RamiroChac0n/P1_ORGA_G-12/Kicad/Práctica1 Lab.kicad_sch

## KiCad design Kicad/Práctica1 Lab.kicad_sch (2024-06-10)

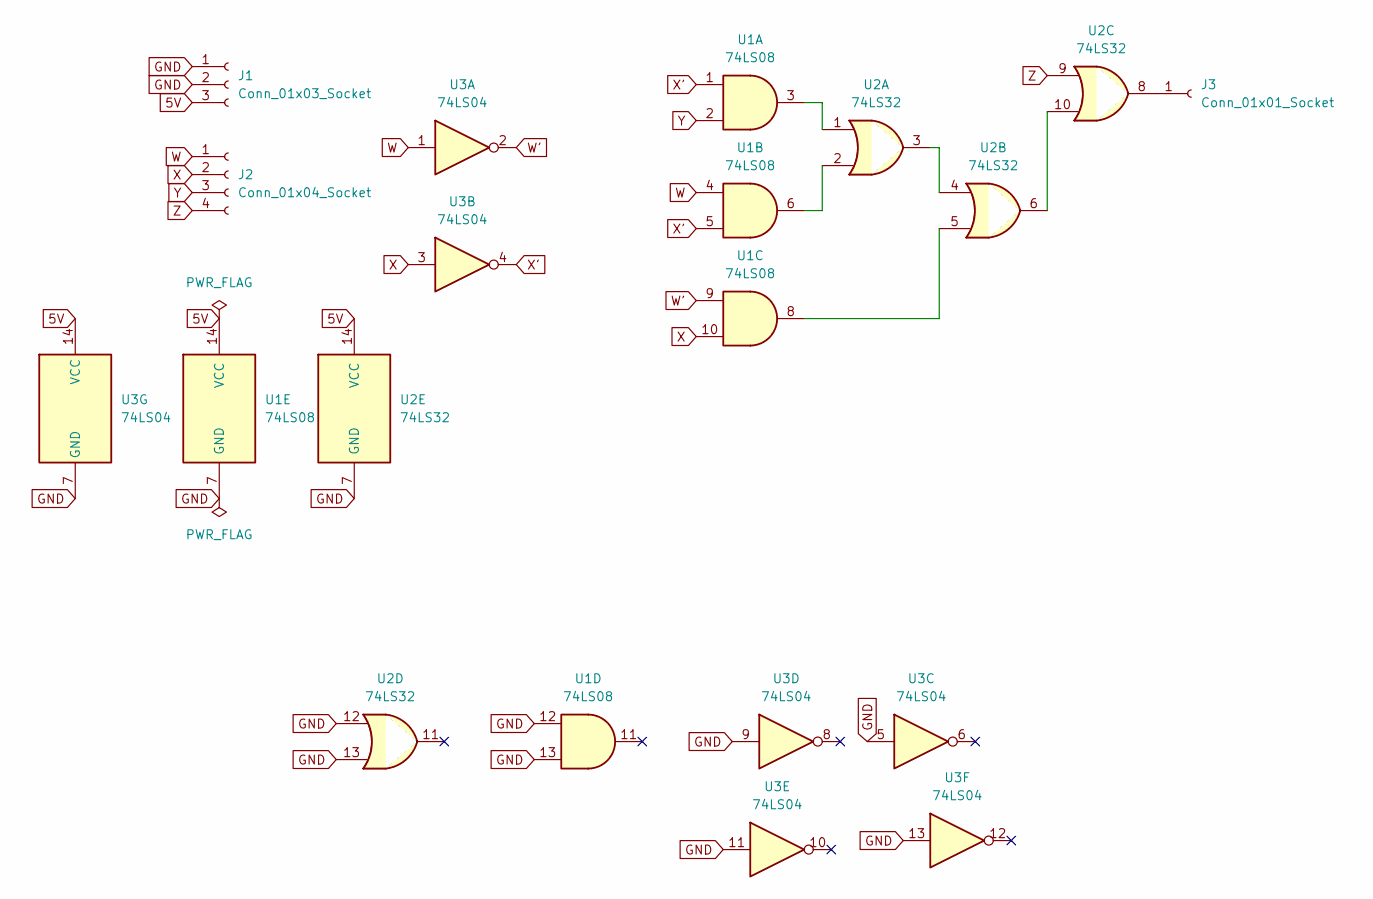
[picture p14: schematic Práctica1 Lab.kicad_sch]

Parts:
J1: Conn_01x03_Socket; PinSocket_1x03_P2.54mm_Vertical
J2: Conn_01x04_Socket; PinSocket_1x04_P2.54mm_Vertical
J3: Conn_01x01_Socket; PinSocket_1x01_P2.54mm_Vertical
U1: 74LS08; DIP-14_W7.62mm_Socket_LongPads
U2: 74LS32; DIP-14_W7.62mm_Socket_LongPads
U3: 74LS04; DIP-14_W7.62mm_Socket_LongPads

Connections:
5V: J1.3, U1.14 (VCC), U2.14 (VCC), U3.14 (VCC)
GND: J1.1, J1.2, U1.7 (GND), U1.12, U1.13, U2.7 (GND), U2.12, U2.13, U3.5, U3.7 (GND), U3.9, U3.11, U3.13
unnamed: J3.1, U2.8
unnamed: U1.3, U2.1
unnamed: U1.6, U2.2
unnamed: U1.8, U2.5
unnamed: U2.3, U2.4
unnamed: U2.6, U2.10
W: J2.1, U1.4, U3.1
W': U1.9, U3.2
X: J2.2, U1.10, U3.3
X': U1.1, U1.5, U3.4
Y: J2.3, U1.2
Z: J2.4, U2.9
